PaoloGolinelli/simple-game-boy-ESP32/circuit S3 mini/component_assembly_bottom_view.png

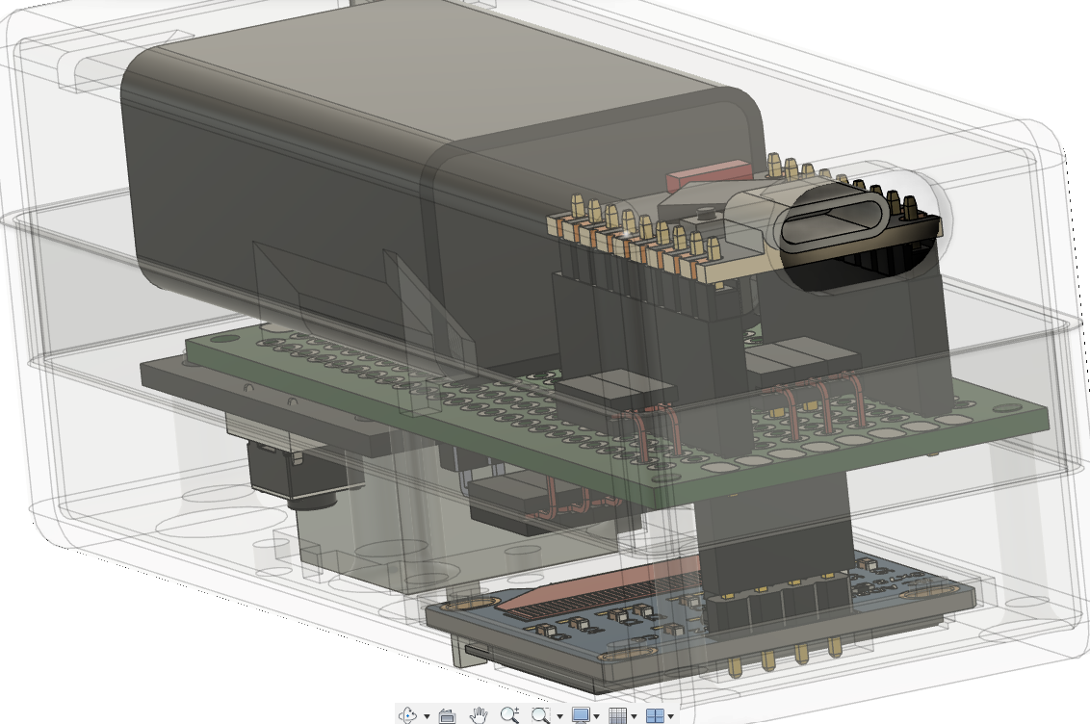
circuit S3 mini/component_assembly_bottom_view.png
